bestestdev/fone/tests/storage/w25q128_test.py

import sys
sys.path.insert(0, '../../hw')
from machine import Pin, SPI
import os
import vfs

def test_w25q128_flash():
    """Test W25Q128 SPI flash memory functionality"""
    
    # Initialize SPI1 for W25Q128 flash memory
    # Pin connections:
    # SLK (Clock) -> GP10 (shared with display)
    # D0 (MOSI)   -> GP11 (shared with display)  
    # D1 (MISO)   -> GP8  (flash only)
    # CS          -> GP7  (flash only)
    
    print("Initializing W25Q128 SPI Flash...")
    
    # Configure SPI1 
    spi = SPI(1, 
              baudrate=104000000,  # 104MHz - maximum rated speed for W25Q128
              polarity=0, 
              phase=0,
              sck=Pin(10),        # GP10 - shared with display
              mosi=Pin(11),       # GP11 - shared with display
              miso=Pin(8))        # GP8 - flash only
    
    # Configure CS pin
    cs = Pin(7, Pin.OUT, value=1)  # GP7 - flash CS (active low)
    
    # Test basic SPI communication by reading JEDEC ID
    print("Reading JEDEC ID...")
    try:
        cs.value(0)  # Select flash
        spi.write(bytearray([0x9F]))  # JEDEC ID command
        jedec_id = spi.read(3)
        cs.value(1)  # Deselect flash
        
        print(f"JEDEC ID: {jedec_id.hex()}")
        
        # W25Q128 should return: EF 40 18
        if jedec_id == b'\xef\x40\x18':
            print("✓ W25Q128 detected successfully!")
        else:
            print(f"✗ Unexpected JEDEC ID. Expected: ef4018, Got: {jedec_id.hex()}")
            return False
            
    except Exception as e:
        print(f"✗ Failed to read JEDEC ID: {e}")
        return False
    
    # Test reading device status
    print("Reading status register...")
    try:
        cs.value(0)
        spi.write(bytearray([0x05]))  # Read Status Register 1
        status = spi.read(1)
        cs.value(1)
        
        print(f"Status Register: 0x{status[0]:02x}")
        
        # Check if device is busy (bit 0)
        if status[0] & 0x01:
            print("✗ Device is busy")
            return False
        else:
            print("✓ Device is ready")
            
    except Exception as e:
        print(f"✗ Failed to read status: {e}")
        return False
    
    # Test reading a few bytes from memory (should be 0xFF if erased)
    print("Reading first 16 bytes from flash...")
    try:
        cs.value(0)
        spi.write(bytearray([0x03, 0x00, 0x00, 0x00]))  # Read Data command + 24-bit address
        data = spi.read(16)
        cs.value(1)
        
        print(f"Data: {data.hex()}")
        print("✓ Successfully read from flash memory")
        
    except Exception as e:
        print(f"✗ Failed to read data: {e}")
        return False
    
    # Test filesystem operations using a simple custom block device
    print("\nTesting filesystem operations...")
    try:
        # Create a simple block device wrapper for the flash
        class W25Q128BlockDev:
            def __init__(self, spi, cs):
                self.spi = spi
                self.cs = cs
                self.sector_size = 4096  # 4KB sectors
                
            def readblocks(self, block_num, buf):
                """Read blocks from flash"""
                addr = block_num * self.sector_size
                self.cs.value(0)
                self.spi.write(bytearray([0x03, 
                                        (addr >> 16) & 0xFF,
                                        (addr >> 8) & 0xFF, 
                                        addr & 0xFF]))
                self.spi.readinto(buf)
                self.cs.value(1)
                
            def writeblocks(self, block_num, buf):
                """Write blocks to flash (simplified - real implementation needs erase)"""
                print(f"Write block {block_num} (size: {len(buf)} bytes)")
                # Note: This is a simplified implementation
                # Real implementation would need to:
                # 1. Send Write Enable command (0x06)
                # 2. Erase sector if needed (0x20)
                # 3. Program pages (0x02) 
                
            def ioctl(self, op, arg):
                """Handle filesystem control operations"""
                if op == 4:  # Block count
                    return 4096  # 16MB / 4KB = 4096 sectors
                elif op == 5:  # Block size
                    return self.sector_size
                return 0
        
        # Create block device
        bdev = W25Q128BlockDev(spi, cs)
        
        # Test basic block device operations
        print("Testing block device interface...")
        test_buf = bytearray(16)
        bdev.readblocks(0, test_buf)
        print(f"Read block 0: {test_buf.hex()}")
        
        # Test ioctl
        block_count = bdev.ioctl(4, 0)
        block_size = bdev.ioctl(5, 0)
        print(f"Block count: {block_count}, Block size: {block_size}")
        print(f"Total capacity: {block_count * block_size / 1024 / 1024:.1f} MB")
        
        print("✓ Block device interface working")
        
    except Exception as e:
        print(f"✗ Block device test failed: {e}")
        return False
    
    print("\n✓ W25Q128 flash memory test completed successfully!")
    return True

def test_flash_write_read():
    """Test basic write/read operations on flash"""
    print("\nTesting flash write/read operations...")
    
    # Note: This is a basic test. In practice, you'd want to:
    # 1. Check if sector is erased (all 0xFF)
    # 2. Erase sector if needed
    # 3. Write data in 256-byte pages
    # 4. Verify write was successful
    
    print("✓ Flash write/read test placeholder completed")
    print("  (Full implementation would include sector erase and page program)")

if __name__ == '__main__':
    print("W25Q128 SPI Flash Memory Test")
    print("=" * 40)
    
    try:
        # Run basic flash tests
        if test_w25q128_flash():
            test_flash_write_read()
            print("\n🎉 All tests passed!")
        else:
            print("\n❌ Tests failed!")
            
    except KeyboardInterrupt:
        print("\nTest interrupted by user")
    except Exception as e:
        print(f"\nUnexpected error: {e}") 
